FreeVario/FreeVarioF1/Doc/IMG_20180330_141803771.jpg

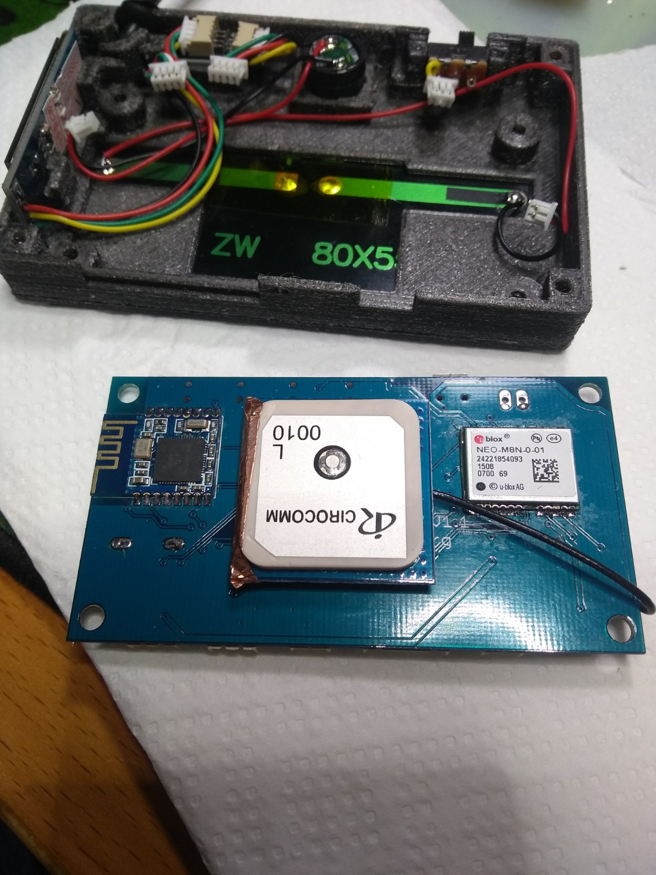
Doc/IMG_20180330_141803771.jpg
