FreeVario/FreeVarioF1/Src/FreeVario/FreeVarioLib/globals.h

/*
 FreeVario http://FreeVario.org

  Copyright (c), PrimalCode (http://www.primalcode.org)
  This program is free software: you can redistribute it and/or modify
  it under the terms of the GNU General Public License as published by
  the Free Software Foundation, either version 3 of the License, or
  any later version. see <http://www.gnu.org/licenses/>
*/

#ifndef GLOBALS_H_
#define GLOBALS_H_



//ALL global references
settings_t conf;
extern I2C_HandleTypeDef FV_I2C1;
#ifdef FV_I2C2
extern I2C_HandleTypeDef FV_I2C2;
#endif
#ifdef FV_UARTGPS
extern UART_HandleTypeDef FV_UARTGPS;
#endif
#ifdef FV_UARTBT
extern UART_HandleTypeDef FV_UARTBT;
#endif
extern IWDG_HandleTypeDef FV_IWDG;

//DHT TIMER
//extern TIM_HandleTypeDef FV_DHTTIMER;

float currentVarioMPS; // ft/s
float cuttentVarioAvMPS;
float currentAltitudeMtr;
int32_t realPressureAv;  // pressure hpa * 100

float accel_x;
float accel_y;
float accel_z;
float gyro_x;
float gyro_y;
float gyro_z;

float humidity;
float humidtemp;

double vbat;
uint8_t pbat;
uint8_t ischarging;
uint8_t ischarged;

extern uint8_t takeoff;

#endif /* GLOBALS_H_ */
