FreeVario/FreeVarioF1/Src/FreeVario/FreeVarioLib/am2322.h

/*
 FreeVario http://FreeVario.org

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
  Code derived from:
  Temperature and Humidity Sensor mbed library
  by 2014 tomozh <tomozh@gmail.com>

*/


#ifndef AM2322_H_
#define AM2322_H_
#include "../Src/config.h"

typedef struct tagRESULT
{
	float temperature;
	float humidity;
}RESULT;



/** Read current temperature and humidity from AM2321
 * @return  result (true=success)
 */
bool AM2322_poll(I2C_HandleTypeDef *FV_AMI2C);

/** Get last read temperature value
 * @return  temperature value (degress)
 */
float AM2322_getTemperature(void);

/** Get last read humidity value
 * @return  humidity value (%RH)
 */
float AM2322_getHumidity(void);


float getLogicalValue(uint16_t regVal);
uint16_t calcCRC16(const uint8_t* src, int len);


RESULT _result;

#endif /* AM2322_H_ */
